AnaviTechnology/anavi-arrows/anavi-arrows.kicad_sch

## KiCad design anavi-arrows.kicad_sch (2023-01-01)

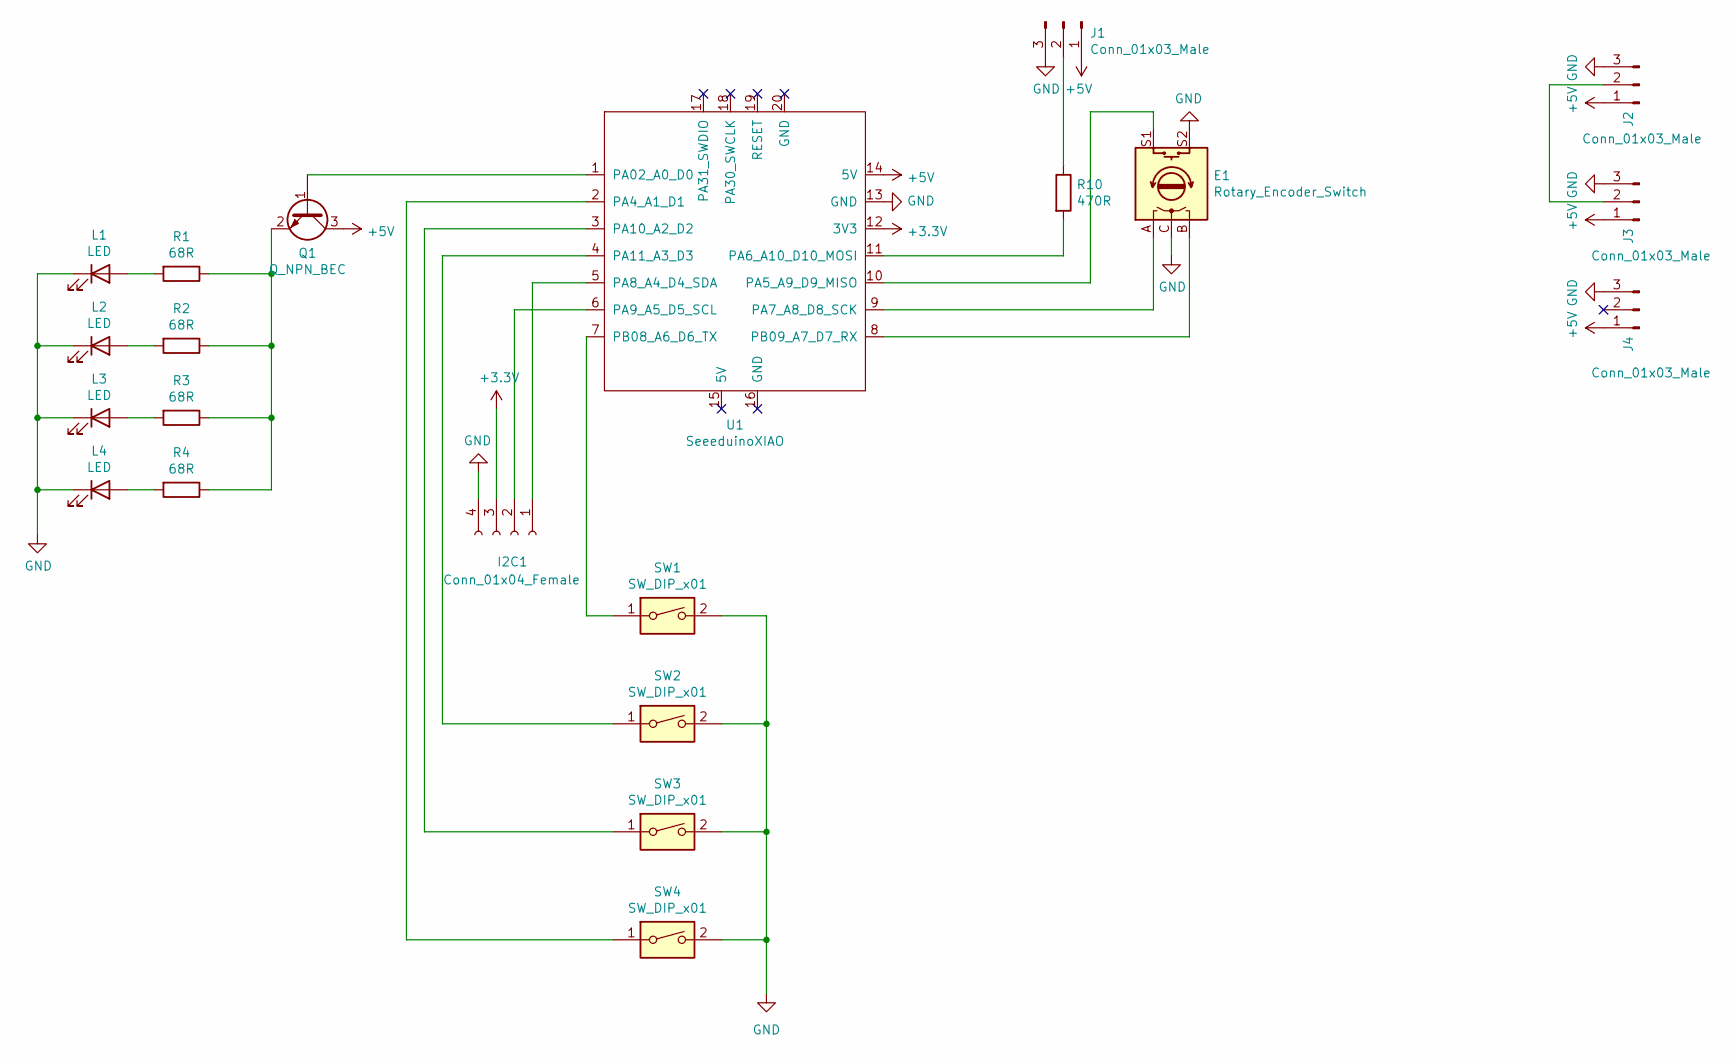
[picture p9: schematic anavi-arrows.kicad_sch]

Parts:
E1: Rotary_Encoder_Switch; RotaryEncoder_Alps_EC11E-Switch_Vertical_H20mm
I2C1: Conn_01x04_Female; PinHeader_1x04_P2.54mm_Vertical
J1, J2, J3, J4: Conn_01x03_Male; LedConnector_1x03_P2.54mm
L1, L2, L3, L4: LED; LED_1206_3216Metric
Q1: Q_NPN_BEC; SOT-23
R1, R2, R3, R4: 68R; R_0603_1608Metric_Pad0.98x0.95mm_HandSolder
R10: 470R; R_0603_1608Metric_Pad0.98x0.95mm_HandSolder
SW1, SW2, SW3, SW4: SW_DIP_x01; Kailh_socket_MX
U1: SeeeduinoXIAO; Seeeduino XIAO-MOUDLE14P-2.54-21X17.8MM

Connections:
+3.3V: I2C1.3, U1.12 (3V3)
+5V: J1.1, J2.1, J3.1, J4.1, Q1.3 (C), U1.14 (5V)
GND: E1.C, E1.S2, I2C1.4, J1.3, J2.3, J3.3, J4.3, L1.1 (K), L2.1 (K), L3.1 (K), L4.1 (K), SW1.2, SW2.2, SW3.2, SW4.2, U1.13 (GND)
unnamed: E1.A, U1.9 (PA7_A8_D8_SCK)
unnamed: E1.B, U1.8 (PB09_A7_D7_RX)
unnamed: E1.S1, U1.10 (PA5_A9_D9_MISO)
unnamed: I2C1.1, U1.5 (PA8_A4_D4_SDA)
unnamed: I2C1.2, U1.6 (PA9_A5_D5_SCL)
unnamed: J1.2, R10.1
unnamed: J2.2, J3.2
unnamed: L1.2 (A), R1.2
unnamed: L2.2 (A), R2.2
unnamed: L3.2 (A), R3.2
unnamed: L4.2 (A), R4.2
unnamed: Q1.1 (B), U1.1 (PA02_A0_D0)
unnamed: Q1.2 (E), R1.1, R2.1, R3.1, R4.1
unnamed: R10.2, U1.11 (PA6_A10_D10_MOSI)
unnamed: SW1.1, U1.7 (PB08_A6_D6_TX)
unnamed: SW2.1, U1.4 (PA11_A3_D3)
unnamed: SW3.1, U1.3 (PA10_A2_D2)
unnamed: SW4.1, U1.2 (PA4_A1_D1)
